akash-siv/Dream-Walker/06-Steam VR Driver/openvr-driver-example-main/OpenVrDriverExample/OpenVrDriverExample/src/ControllerDriver.cpp

#include <ControllerDriver.h>

EVRInitError ControllerDriver::Activate(uint32_t unObjectId)
{
	driverId = unObjectId; //unique ID for your driver

	PropertyContainerHandle_t props = VRProperties()->TrackedDeviceToPropertyContainer(driverId); //this gets a container object where you store all the information about your driver

	VRProperties()->SetStringProperty(props, Prop_InputProfilePath_String, "{example}/input/controller_profile.json"); //tell OpenVR where to get your driver's Input Profile
	VRProperties()->SetInt32Property(props, Prop_ControllerRoleHint_Int32, ETrackedControllerRole::TrackedControllerRole_Treadmill); //tells OpenVR what kind of device this is
	VRDriverInput()->CreateScalarComponent(props, "/input/joystick/y", &joystickYHandle, EVRScalarType::VRScalarType_Absolute,
		EVRScalarUnits::VRScalarUnits_NormalizedTwoSided); //sets up handler you'll use to send joystick commands to OpenVR with, in the Y direction (forward/backward)
	VRDriverInput()->CreateScalarComponent(props, "/input/trackpad/y", &trackpadYHandle, EVRScalarType::VRScalarType_Absolute,
		EVRScalarUnits::VRScalarUnits_NormalizedTwoSided); //sets up handler you'll use to send trackpad commands to OpenVR with, in the Y direction
	VRDriverInput()->CreateScalarComponent(props, "/input/joystick/x", &joystickXHandle, EVRScalarType::VRScalarType_Absolute,
		EVRScalarUnits::VRScalarUnits_NormalizedTwoSided); //Why VRScalarType_Absolute? Take a look at the comments on EVRScalarType.
	VRDriverInput()->CreateScalarComponent(props, "/input/trackpad/x", &trackpadXHandle, EVRScalarType::VRScalarType_Absolute,
		EVRScalarUnits::VRScalarUnits_NormalizedTwoSided); //Why VRScalarUnits_NormalizedTwoSided? Take a look at the comments on EVRScalarUnits.
	
	//The following properites are ones I tried out because I saw them in other samples, but I found they were not needed to get the sample working.
	//There are many samples, take a look at the openvr_header.h file. You can try them out.

	//VRProperties()->SetUint64Property(props, Prop_CurrentUniverseId_Uint64, 2);
	//VRProperties()->SetBoolProperty(props, Prop_HasControllerComponent_Bool, true);
	//VRProperties()->SetBoolProperty(props, Prop_NeverTracked_Bool, true);
	//VRProperties()->SetInt32Property(props, Prop_Axis0Type_Int32, k_eControllerAxis_TrackPad);
	//VRProperties()->SetInt32Property(props, Prop_Axis2Type_Int32, k_eControllerAxis_Joystick);
	//VRProperties()->SetStringProperty(props, Prop_SerialNumber_String, "example_controler_serial");
	//VRProperties()->SetStringProperty(props, Prop_RenderModelName_String, "vr_controller_vive_1_5");
	//uint64_t availableButtons = ButtonMaskFromId(k_EButton_SteamVR_Touchpad) |
	//	ButtonMaskFromId(k_EButton_IndexController_JoyStick);
	//VRProperties()->SetUint64Property(props, Prop_SupportedButtons_Uint64, availableButtons);

	return VRInitError_None;
}

DriverPose_t ControllerDriver::GetPose()
{
	DriverPose_t pose = { 0 }; //This example doesn't use Pose, so this method is just returning a default Pose.
	pose.poseIsValid = false;
	pose.result = TrackingResult_Calibrating_OutOfRange;
	pose.deviceIsConnected = true;

	HmdQuaternion_t quat;
	quat.w = 1;
	quat.x = 0;
	quat.y = 0;
	quat.z = 0;

	pose.qWorldFromDriverRotation = quat;
	pose.qDriverFromHeadRotation = quat;

	return pose;
}


const float STOPPED = 0.0;
const float WALK_SPEED = 0.2;
const float RUN_SPEED = 0.5;

void ControllerDriver::RunFrame()
{
	// Set movement speed.
	float currMovSpeed = WALK_SPEED;
	if (GetKeyState('R') & 0x8000) {
		currMovSpeed = RUN_SPEED;
	}

	// Direction of movement.
	if (GetKeyState('W') & 0x8000) {
		VRDriverInput()->UpdateScalarComponent(joystickYHandle, currMovSpeed, 0);
		VRDriverInput()->UpdateScalarComponent(trackpadYHandle, currMovSpeed, 0);
	}
	else if (GetKeyState('S') & 0x8000) {
		VRDriverInput()->UpdateScalarComponent(joystickYHandle, -currMovSpeed, 0);
		VRDriverInput()->UpdateScalarComponent(trackpadYHandle, -currMovSpeed, 0);
	}
	else if (!(
		(GetKeyState('W') & 0x8000) &&
		(GetKeyState('S') & 0x8000)
		)) {
		VRDriverInput()->UpdateScalarComponent(joystickYHandle, 0.0f, 0); //move forward
		VRDriverInput()->UpdateScalarComponent(trackpadYHandle, 0.0f, 0); //move foward
	}

	// We can also move sideways.
	if (GetKeyState('A') & 0x8000) {
		VRDriverInput()->UpdateScalarComponent(joystickXHandle, -currMovSpeed, 0);
		VRDriverInput()->UpdateScalarComponent(trackpadXHandle, -currMovSpeed, 0);
	}
	else if (GetKeyState('D') & 0x8000) {
		VRDriverInput()->UpdateScalarComponent(joystickXHandle, currMovSpeed, 0);
		VRDriverInput()->UpdateScalarComponent(trackpadXHandle, currMovSpeed, 0);
	}
	else if (!(
		(GetKeyState('A') & 0x8000) &&
		(GetKeyState('D') & 0x8000)
		)) {
		VRDriverInput()->UpdateScalarComponent(joystickXHandle, 0.0f, 0);
		VRDriverInput()->UpdateScalarComponent(trackpadXHandle, 0.0f, 0);
	}

}

void ControllerDriver::Deactivate()
{
	driverId = k_unTrackedDeviceIndexInvalid;
}

void* ControllerDriver::GetComponent(const char* pchComponentNameAndVersion)
{
	//I found that if this method just returns null always, it works fine. But I'm leaving the if statement in since it doesn't hurt.
	//Check out the IVRDriverInput_Version declaration in openvr_driver.h. You can search that file for other _Version declarations 
	//to see other components that are available. You could also put a log in this class and output the value passed into this 
	//method to see what OpenVR is looking for.
	if (strcmp(IVRDriverInput_Version, pchComponentNameAndVersion) == 0)
	{
		return this;
	}
	return NULL;
}

void ControllerDriver::EnterStandby() {}

void ControllerDriver::DebugRequest(const char* pchRequest, char* pchResponseBuffer, uint32_t unResponseBufferSize) 
{
	if (unResponseBufferSize >= 1)
	{
		pchResponseBuffer[0] = 0;
	}
}
